gcduino/gcduinode/Arduino/MailBox_btns/Reference.ino

/*
NODE Addresses:
1 = Base Station
2 = Door Bell/NFC (Planned)
3 = Mail Box      (Planned)

Senor Number & Type:                   Note: I'm want to try keep all the different sensor types on a indivdual Number
1 = TMP36
2 = LDR to 10k Divider
3 = Hall Effect (Door, Mail box etc)
4 = CRT1000 Prox Sensor
5 = PIR


*/
